BzowK/RealPKEMeter/Model/Modified-115_5mm (Old)/BottomFront.stl

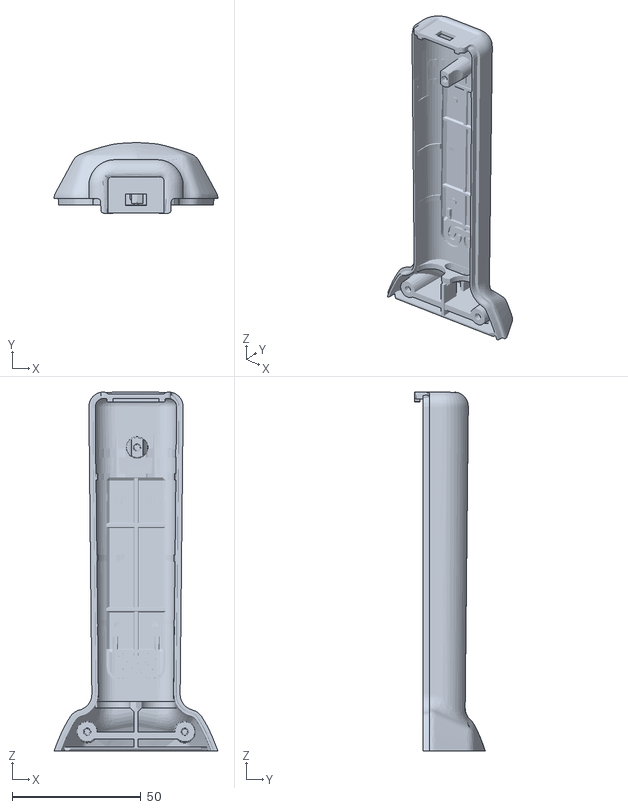
[picture p17: CAD file, 2020-10-29, an earlier design]
Model/Modified-115_5mm (Old)/BottomFront.stl
63.6 x 27.4 x 139.4
