BzowK/RealPKEMeter/Model/Modified-115_5mm (Old)/WingTops.stl

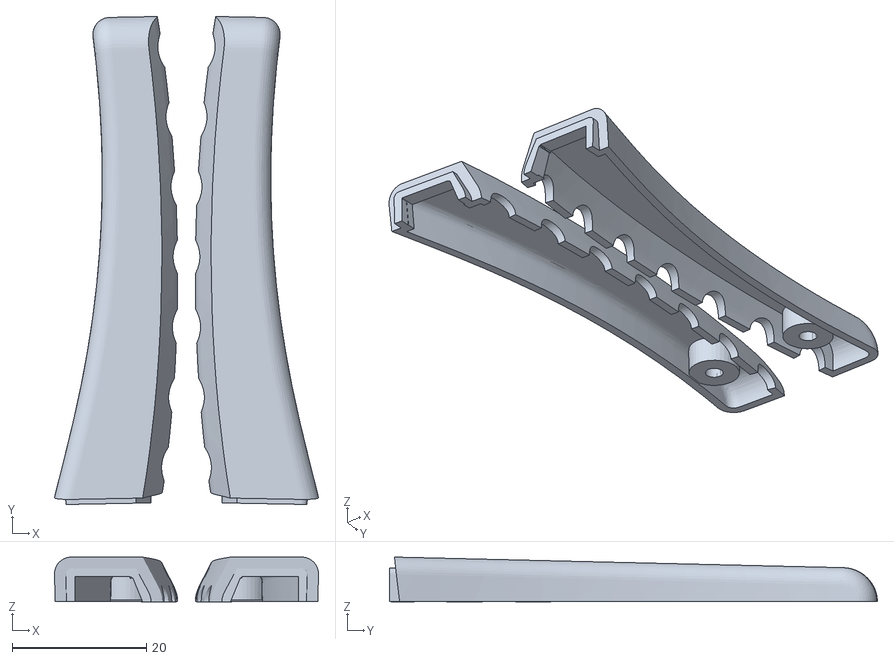
[picture p18: CAD file, 2020-10-29, an earlier design]
Model/Modified-115_5mm (Old)/WingTops.stl
39.4 x 72.8 x 6.70
